CaseyTea/cmdeck/enclosure/exports/STL/00_shell/CMDECK_KB_BACK_IO_PLATE.stl

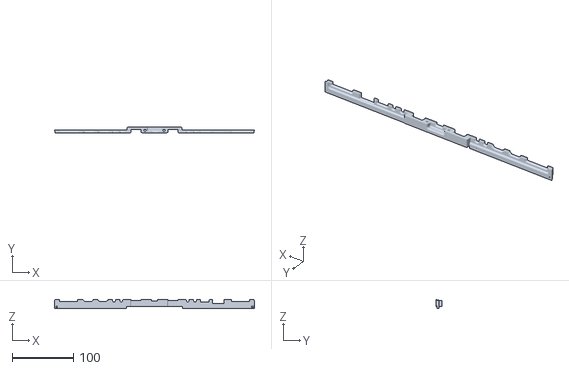
[picture p17: CAD file, 2026-02-10]
enclosure/exports/STL/00_shell/CMDECK_KB_BACK_IO_PLATE.stl
326.0 x 9.15 x 14.4
