CaseyTea/cmdeck/enclosure/exports/STL/02_support structure/CDMDECK_KB_INTERNAL_SUP_TRACKPAD_SHELL.stl

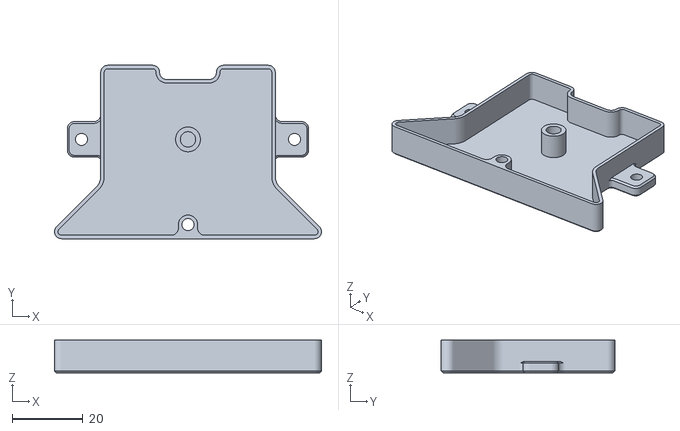
[picture p18: CAD file, 2026-02-10]
enclosure/exports/STL/02_support structure/CDMDECK_KB_INTERNAL_SUP_TRACKPAD_SHELL.stl
75.2 x 48.9 x 9.25
