CaseyTea/cmdeck/enclosure/exports/STL/03_controls/CMDECK_KB_LIGHT_PIPE.stl

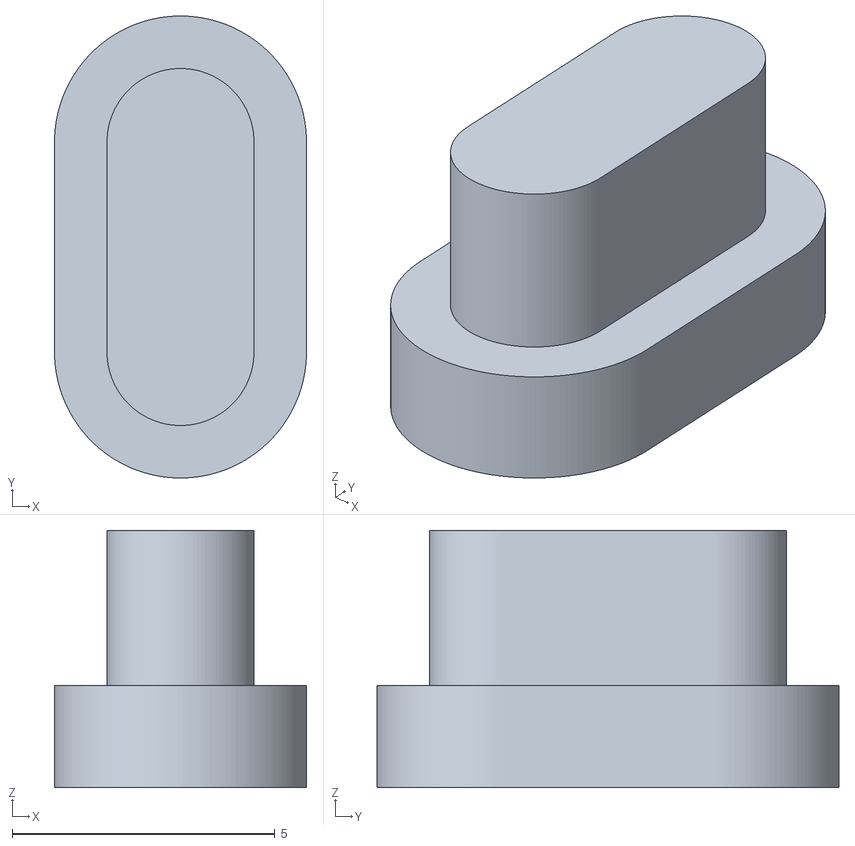
[picture p19: CAD file, 2026-02-10]
enclosure/exports/STL/03_controls/CMDECK_KB_LIGHT_PIPE.stl
4.80 x 8.80 x 4.90
