CaseyTea/cmdeck/enclosure/exports/STL/05_misc/CMDECK_KB_SPEAKER_GRILL.stl

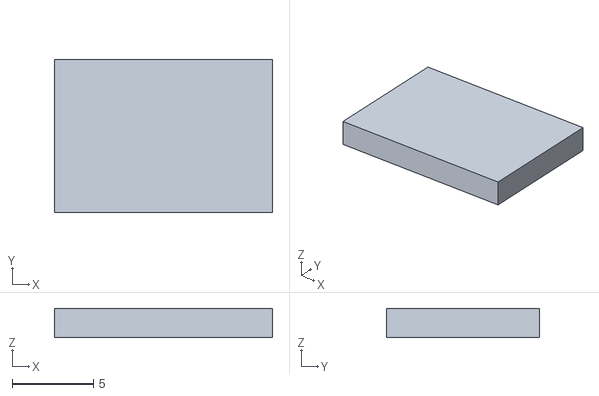
[picture p20: CAD file, 2026-02-10]
enclosure/exports/STL/05_misc/CMDECK_KB_SPEAKER_GRILL.stl
13.4 x 9.40 x 1.80
