CaseyTea/cmdeck/enclosure/exports/STL/02_support structure/CDMDECK_KB_INTERNAL_SUP_BAT_LEFT.stl

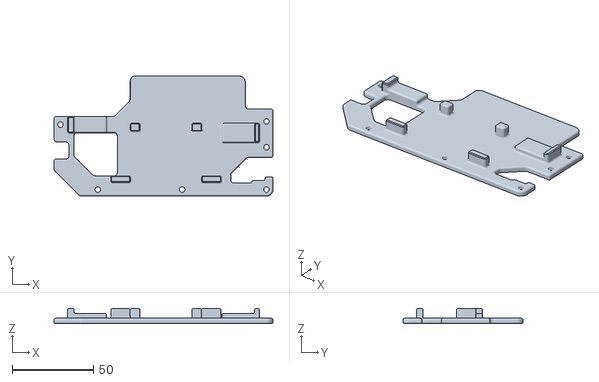
[picture p21: CAD file, 2026-02-10]
enclosure/exports/STL/02_support structure/CDMDECK_KB_INTERNAL_SUP_BAT_LEFT.stl
135.0 x 74.0 x 9.25
