CaseyTea/cmdeck/enclosure/exports/STL/05_misc/CMDECK_WEIGHT_1.stl

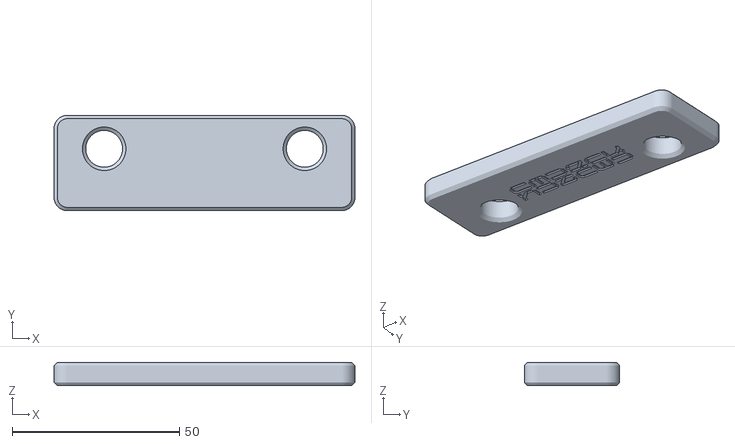
[picture p22: CAD file, 2026-02-10]
enclosure/exports/STL/05_misc/CMDECK_WEIGHT_1.stl
90.0 x 28.5 x 7.00
