CaseyTea/cmdeck/enclosure/exports/STL/02_support structure/CDMDECK_KB_INTERNAL_SUP_STRUC_LEFT.stl

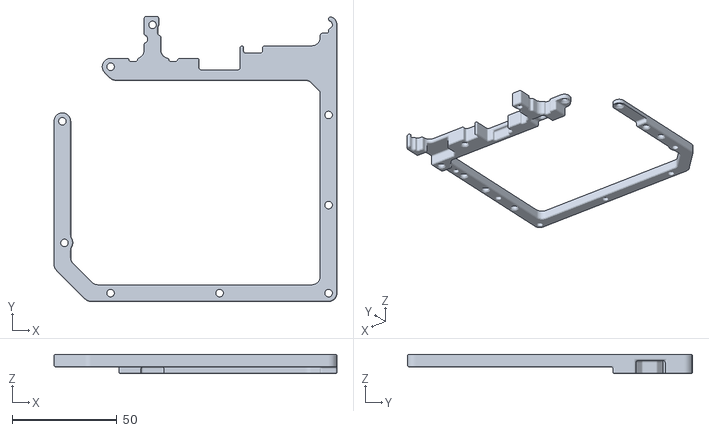
[picture p23: CAD file, 2026-02-10]
enclosure/exports/STL/02_support structure/CDMDECK_KB_INTERNAL_SUP_STRUC_LEFT.stl
135.0 x 136.0 x 9.25
