CaseyTea/cmdeck/enclosure/exports/STL/05_misc/CMDECK_WEIGHT_2.stl

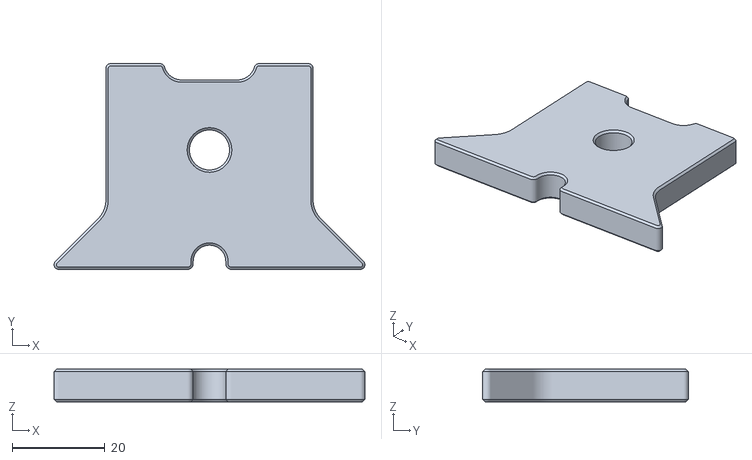
[picture p24: CAD file, 2026-02-10]
enclosure/exports/STL/05_misc/CMDECK_WEIGHT_2.stl
66.9 x 44.3 x 7.00
