CaseyTea/cmdeck/enclosure/exports/STL/02_support structure/CMDECK_KB_OLED_SUPPORT_PIN.stl

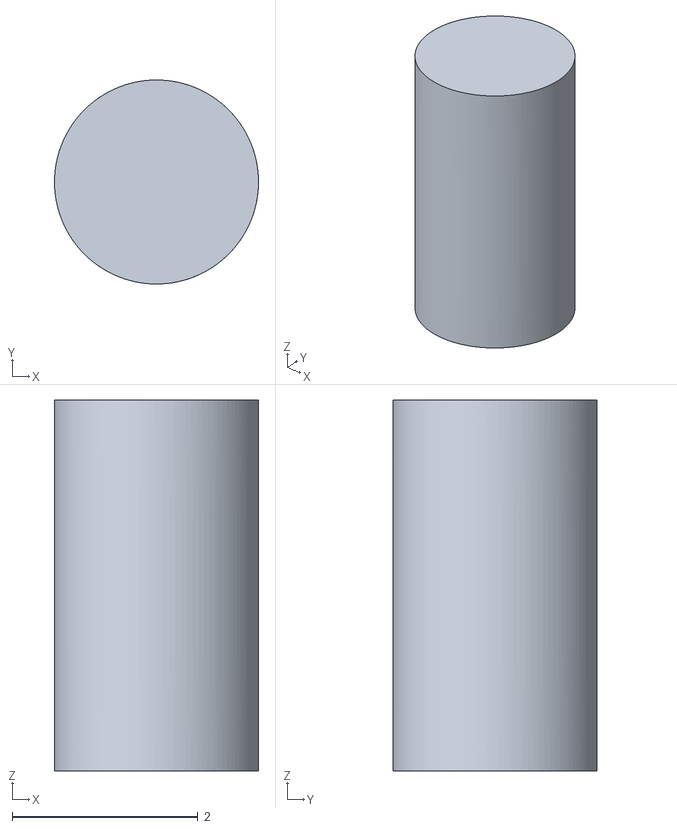
[picture p25: CAD file, 2026-02-10]
enclosure/exports/STL/02_support structure/CMDECK_KB_OLED_SUPPORT_PIN.stl
2.20 x 2.20 x 4.00
