CaseyTea/cmdeck/enclosure/exports/STL/02_support structure/CMDECK_KB_OLED_SUPPORT.stl

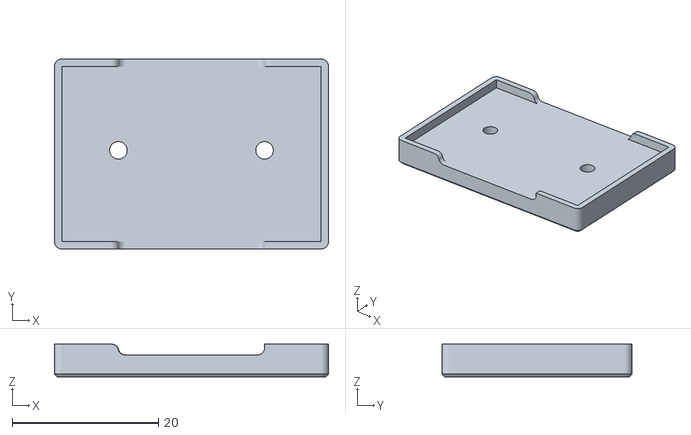
[picture p26: CAD file, 2026-02-10]
enclosure/exports/STL/02_support structure/CMDECK_KB_OLED_SUPPORT.stl
37.5 x 26.0 x 4.50
