CaseyTea/cmdeck/enclosure/exports/STL/05_misc/CMDECK_COOLER_SHROUD.stl

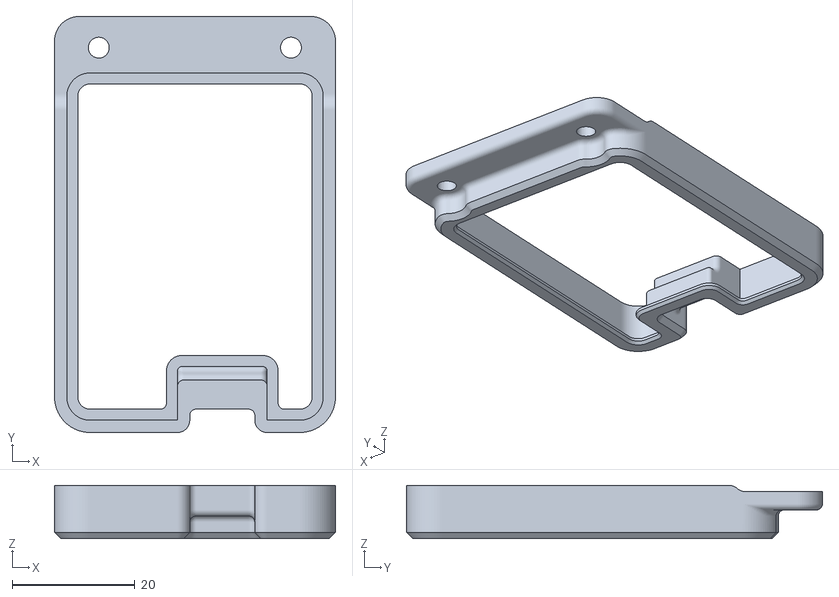
[picture p27: CAD file, 2026-02-10]
enclosure/exports/STL/05_misc/CMDECK_COOLER_SHROUD.stl
45.8 x 67.8 x 8.67
